Instantium/PicoMidiLeds/board/pico-midi-leds/pico-midi-leds.kicad_sch

## KiCad design board/pico-midi-leds/pico-midi-leds.kicad_sch (2024-02-10)

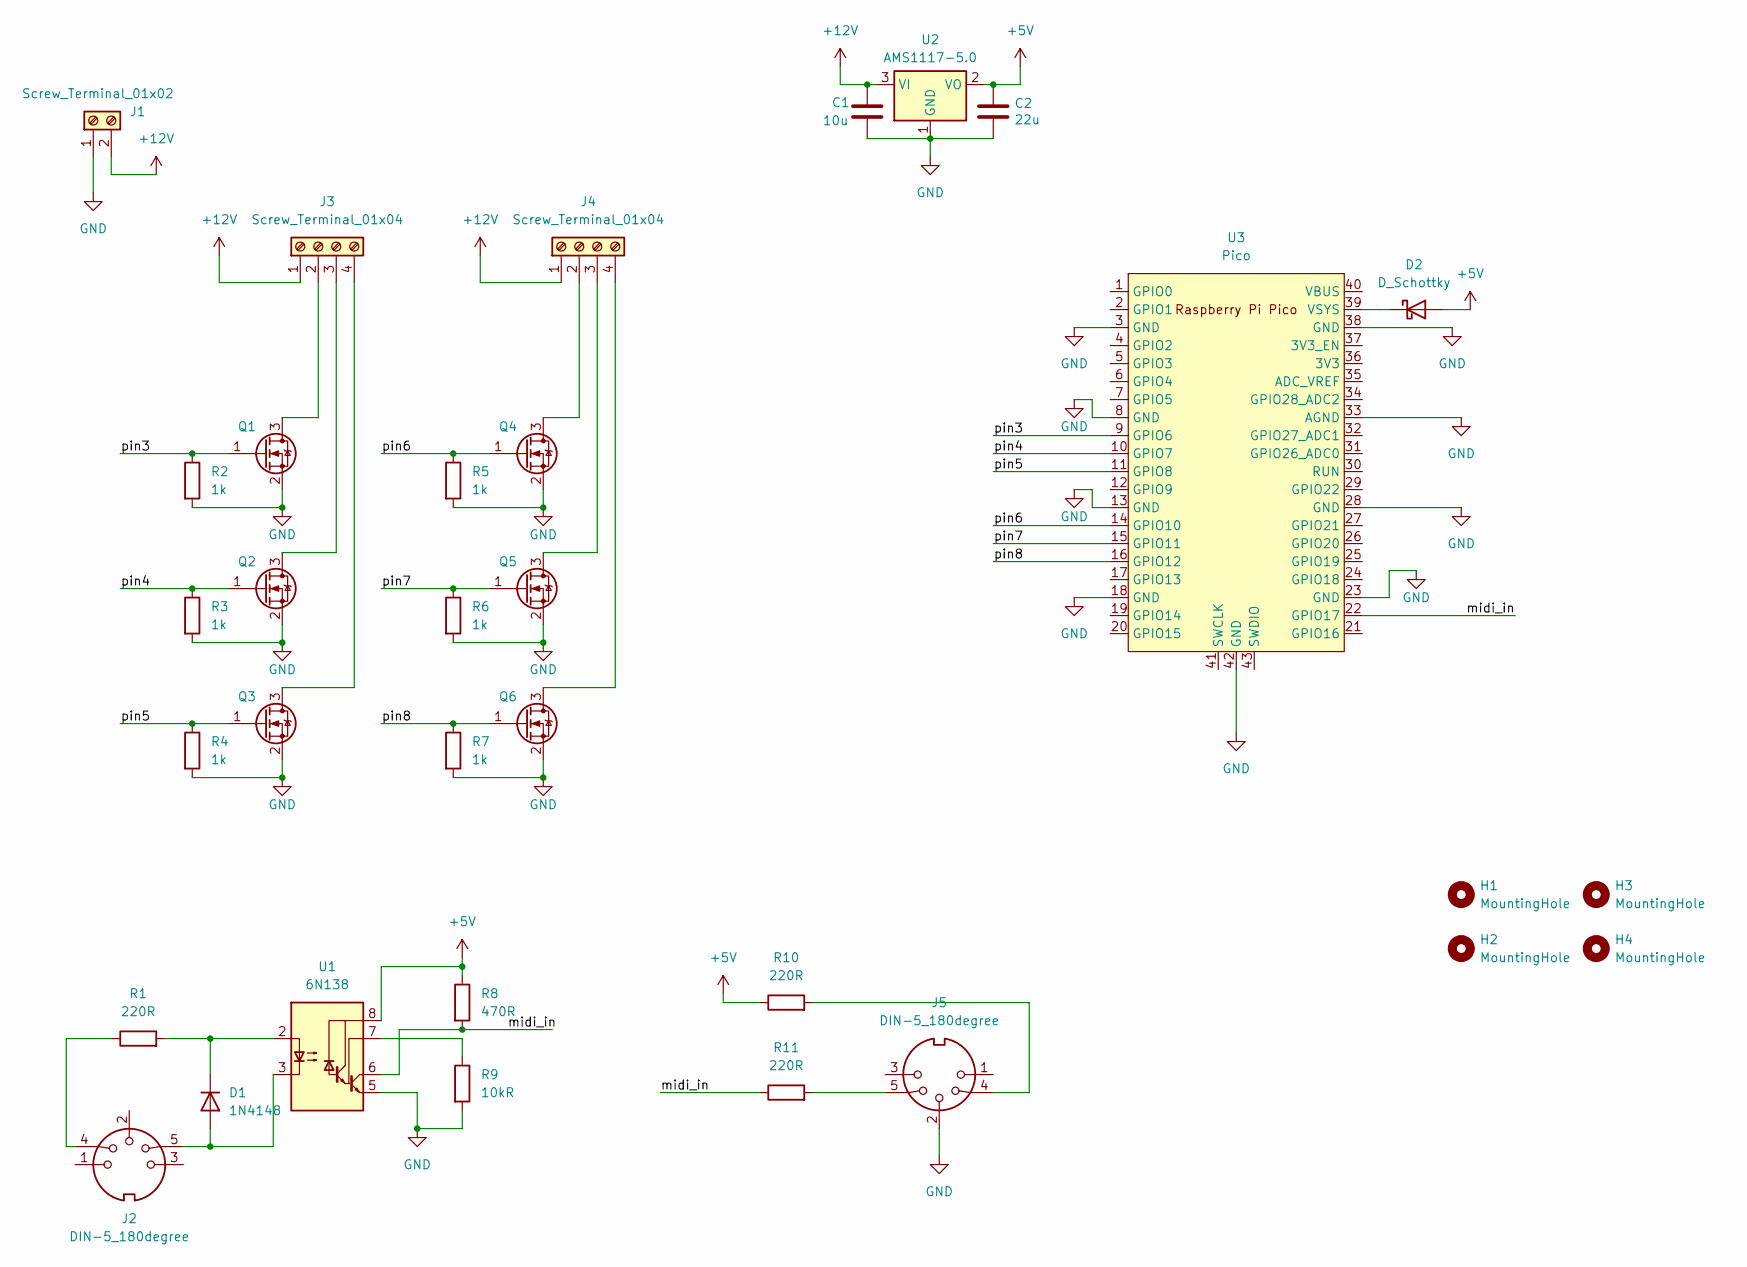
[picture p6: schematic pico-midi-leds.kicad_sch]

Parts:
C1: 10u; C_0805_2012Metric
C2: 22u; C_0805_2012Metric
D1: 1N4148; D_SOD-123
D2: D_Schottky; D_SOD-123
H1, H2, H3, H4: MountingHole
J1: Screw_Terminal_01x02; TerminalBlock_bornier-2_P5.08mm
J2, J5: DIN-5_180degree; din-504-M10; LCSC C2939344
J3, J4: Screw_Terminal_01x04; TerminalBlock_bornier-4_P5.08mm
Q1, Q2, Q3, Q4, Q5, Q6: IRLZ44N; SOT-23
R1, R10, R11: 220R; R_0805_2012Metric_Pad1.20x1.40mm_HandSolder
R2, R3, R4, R5, R6, R7: 1k; R_0805_2012Metric_Pad1.20x1.40mm_HandSolder
R8: 470R; R_0805_2012Metric_Pad1.20x1.40mm_HandSolder
R9: 10kR; R_0805_2012Metric_Pad1.20x1.40mm_HandSolder
U1: 6N138; DIP-8_W7.62mm
U2: AMS1117-5.0; SOT-223-3_TabPin2
U3: Pico; RPi_Pico_SMD_TH

Connections:
+5V: C2.1, D2.2 (A), R8.1, R10.1, U1.8 (VCC), U2.2 (VO)
+12V: C1.1, J1.2, J3.1, J4.1, U2.3 (VI)
GND: C1.2, C2.2, J1.1, J5.2, Q1.2 (S), Q2.2 (S), Q3.2 (S), Q4.2 (S), Q5.2 (S), Q6.2 (S), R2.2, R3.2, R4.2, R5.2, R6.2, R7.2, R9.2, U1.5 (GND), U2.1 (GND), U3.3 (GND), U3.8 (GND), U3.13 (GND), U3.18 (GND), U3.23 (GND), U3.28 (GND), U3.33 (AGND), U3.38 (GND), U3.42 (GND)
unnamed: D1.1 (K), R1.2, U1.2 (C1)
unnamed: D1.2 (A), J2.5, U1.3 (C2)
unnamed: D2.1 (K), U3.39 (VSYS)
unnamed: J2.4, R1.1
unnamed: J3.2, Q1.3 (D)
unnamed: J3.3, Q2.3 (D)
unnamed: J3.4, Q3.3 (D)
unnamed: J4.2, Q4.3 (D)
unnamed: J4.3, Q5.3 (D)
unnamed: J4.4, Q6.3 (D)
unnamed: J5.4, R10.2
unnamed: J5.5, R11.2
unnamed: R9.1, U1.7 (VO1)
midi_in: R8.2, R11.1, U1.6 (VO2), U3.22 (GPIO17)
pin3: Q1.1 (G), R2.1, U3.9 (GPIO6)
pin4: Q2.1 (G), R3.1, U3.10 (GPIO7)
pin5: Q3.1 (G), R4.1, U3.11 (GPIO8)
pin6: Q4.1 (G), R5.1, U3.14 (GPIO10)
pin7: Q5.1 (G), R6.1, U3.15 (GPIO11)
pin8: Q6.1 (G), R7.1, U3.16 (GPIO12)
